FSund/pteron-keyboard/images/38key-switch-plate-square-holes.png

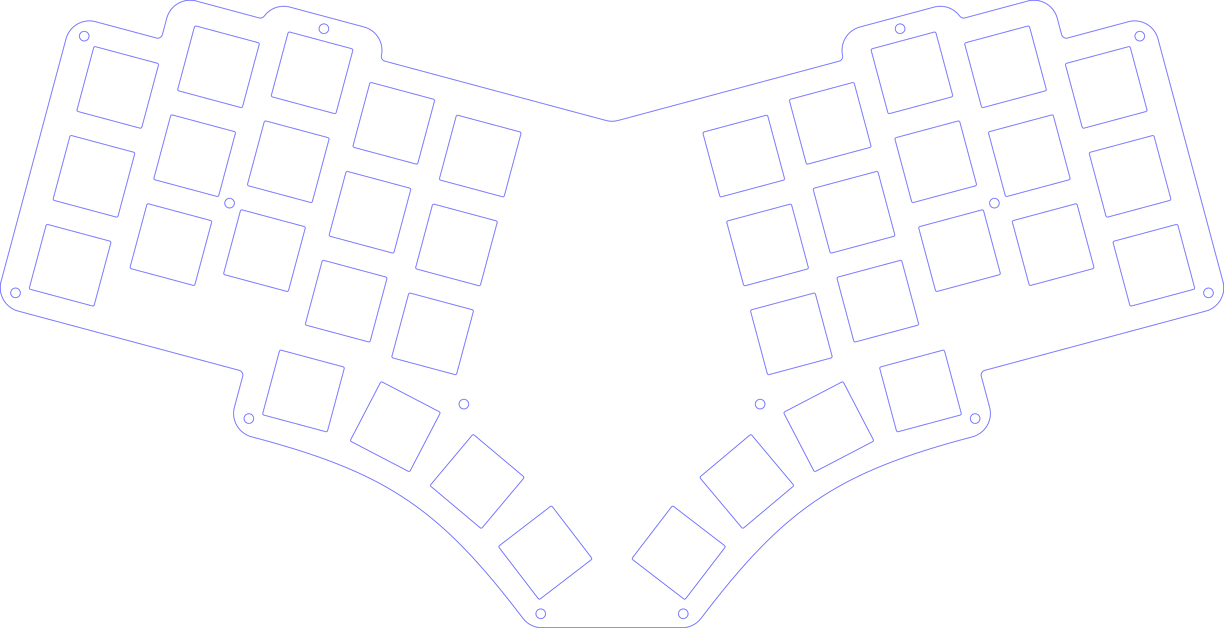
images/38key-switch-plate-square-holes.png
