FSund/pteron-keyboard/images/44key-back-plate.png

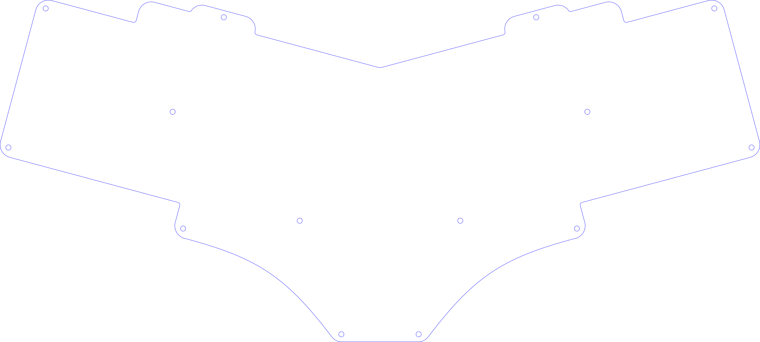
images/44key-back-plate.png
