FSund/pteron-keyboard/images/44key-switch-plate-square-holes.png

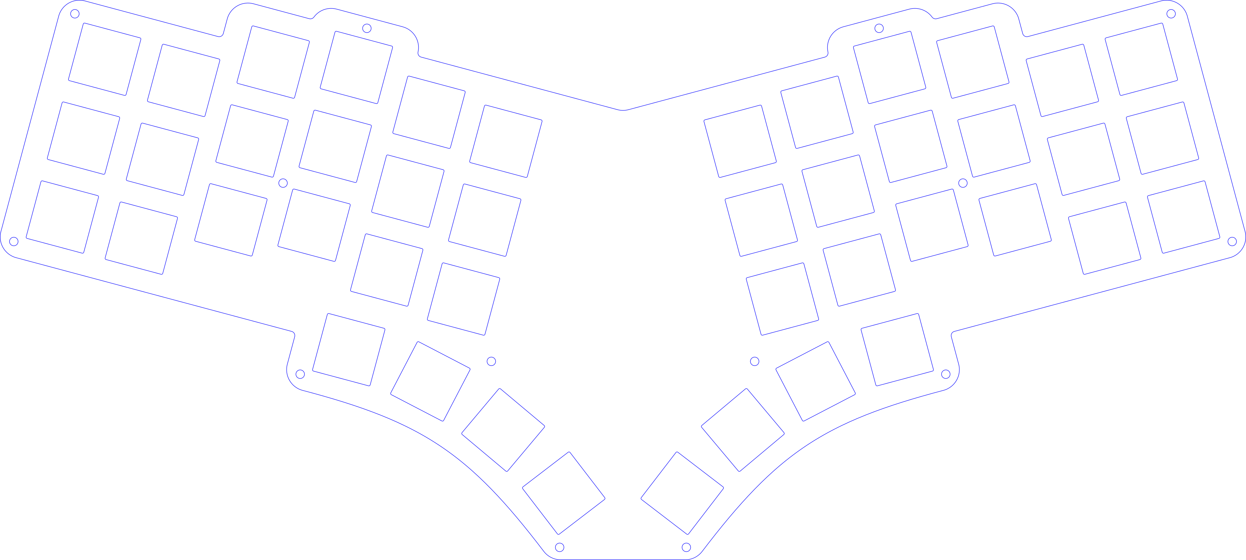
images/44key-switch-plate-square-holes.png
