FSund/pteron-keyboard/images/44key-switch-plate.png

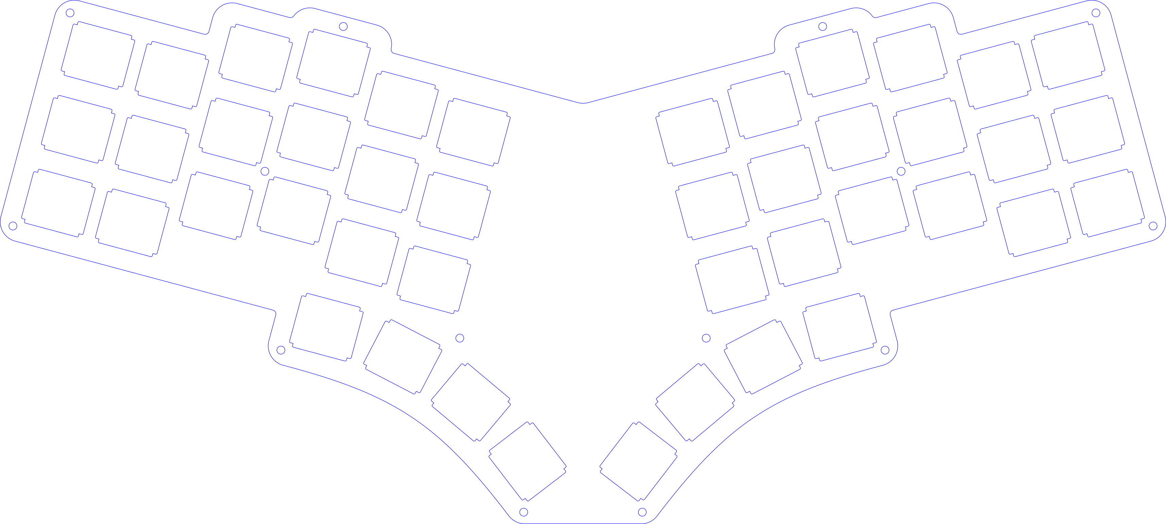
images/44key-switch-plate.png
