FSund/pteron-keyboard/images/56key-back-plate.png

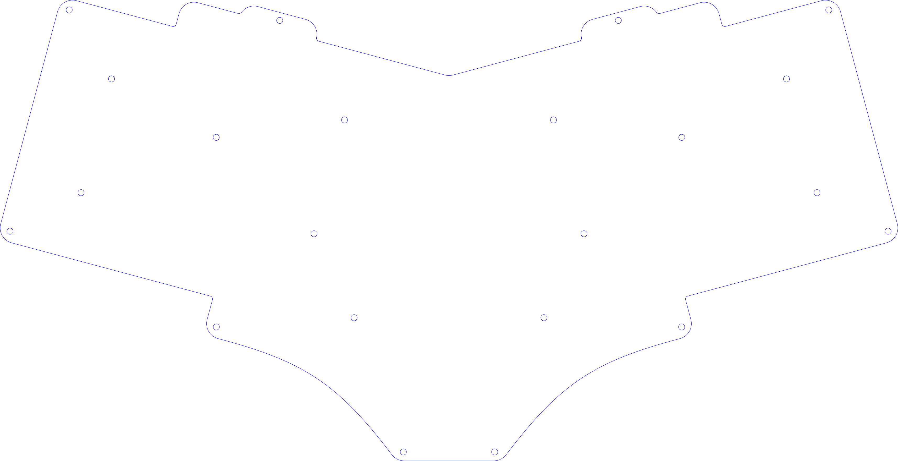
images/56key-back-plate.png
